joshua-p-williams/ls-pcv-system/docs/open-questions.md

# Open questions

This register coordinates follow-up for unresolved hardware checks and design choices. Component and interface pages retain technical details and final decisions; [project status](status.md) summarizes progress. A documented interface is not a verified connection.

## Start here for W01

**Q01 is resolved:** W01 will define the complete bench wiring for the controller, display, ADC, sensor and conditioning, with phased assembly and verification against that design. See the [W01 scope and assembly approach](../hardware/wiring/README.md#w01-scope-and-assembly). **Q02 is resolved:** W01 uses the N16R8 development board; the XIAO remains the finished-gauge target with its own wiring and verification. **Q03 is resolved:** use one USB source at a time, accepting restart when switching between computer and standalone supply. The N16R8 board has not yet arrived: **Q04** normal board comparison and Q05/Q12 bring-up measurements await receipt; Q30/Q31 resolve the intended bench/display power connections. Q15 selects one multifunction button; Q24 selects the initial gesture mapping. Q23 selects fixed brightness initially with provision for later software configuration and persistent settings. Continue the remaining hardware and wiring choices while retaining provisional hardware assumptions.

The complete bench design requires **Q04-Q10, Q12, Q14-Q18 and Q29** as applicable to the selected controller and interfaces. Converter-powered operation adds **Q11 and Q19**. XIAO-specific **Q13** applies only if that board is used. **Q20-Q22** concern operational validation or later vehicle work; they do not all block drafting a bench harness.

[W01 is now a complete-scope draft](../hardware/wiring/bench/README.md), with proposed assignments, explicit unresolved boundaries and derived assembly views. Assembly-ready connections require the relevant evidence. Tests needing a wired fixture follow verification of its terminal mapping and electrical limits; the register does not require a finished gauge before designing that fixture.

## Design decisions

| ID | Question | How to resolve | Blocks / applies to | Status | Reference / recorded answer |
| --- | --- | --- | --- | --- | --- |
| Q01 | ~~Does W01 begin with controller/display only, or include the ADC and sensor?~~ | Scope selected; retain separate verification questions | W01 scope | Resolved | Complete bench wiring design, including ADC/sensor/conditioning; phased assembly with sectional views and checks derived from the same design. Unknowns marked inline with question IDs. [Recorded approach](../hardware/wiring/README.md#w01-scope-and-assembly) |
| Q02 | ~~Will W01 use the planned N16R8 bench board or a XIAO?~~ | Controller selected; physical verification remains open | W01 controller and pin map | Resolved | N16R8 for W01; XIAO for the finished gauge. Both need complete wiring and phased verification, with explicit firmware board configurations. [Wiring approach](../hardware/wiring/README.md#controller-configurations), [firmware requirements](../firmware/README.md#board-configurations) |
| Q03 | ~~Which power/programming mode will the first bench build use?~~ | Operating choice selected; verify implementation under Q05/Q12 | W01 power topology | Resolved | One USB source at a time: computer for power/debugging or suitable standalone USB supply. Unplugging and restart are acceptable. Full-system USB capacity remains unverified. [Bench power requirements](../hardware/wiring/README.md#bench-power-requirements) |
| Q14 | Which GPIOs serve SPI, I2C, display control and any buttons or ADC-ready signal? | Check the proposed allocation against the actual carrier and preserve memory/boot/debug restrictions; maintain explicit GPIOs in the harness | W01 selected interfaces; XIAO allocation separately | Investigating | [W01 proposed controller table](../hardware/wiring/bench/generated/connections.md#proposed-controller-assignments) allocates eight GPIOs for display, I2C and one button; ALERT is unused under the polling proposal. Actual-board verification pending; [P02](../hardware/pinouts/xiao-esp32s3.md) remains separate |
| Q15 | ~~How many user buttons are included?~~ | Button count selected; original gesture/dimming portions tracked separately as Q24/Q23 | W01 control wiring and pin budget | Resolved | One multifunction button, with BetterButton as the planned input library. GPIO and physical switch remain pending. [Control design](../firmware/README.md#multifunction-button) |
| Q16 | ~~What construction and connection approach should the bench harness use?~~ | Construction policy selected; electrical wire requirements and return routing remain W01 design work | W01 construction guidance | Resolved | On-hand nominal 2.54 mm protoboard/header/socket construction. Use soldered leads or secure removable connections at assembler discretion, with support and strain relief. W01 specifies connectivity and electrical constraints; the build record captures chosen connectors, orientation and lengths. [Recorded requirements](../hardware/wiring/README.md#bench-construction-and-retention) |
| Q17 | How will the selected sensor-input circuit behave, and is further protection needed? | Record actual stock R1/C1; check DC loading, response/noise and shared-supply startup/shutdown; determine any additional protection from the actual operating/fault conditions | Pressure-chain assembly/validation | Investigating | Initial [RC filter](../hardware/components/rc-input-filter/README.md) selected: 470 ohm series, 1 uF nonpolar from OUT to GND, IN/OUT/GND nodes in W01. No divider, buffer or clamp selected; nominal design is not measured performance |
| Q18 | What ADC address, gain, rate, mode and readiness method will be used? | Review the candidate against verified module configuration and signal range, then test fresh-conversion timing | ADC wiring where affected; acquisition bring-up | Investigating | [W01 candidate](../hardware/wiring/bench/README.md#adc-bring-up-candidate): A0 single-ended, ADDR-to-GND / 0x48, selected +/-6.144 V, candidate single-shot 128 SPS, 100 kHz translated I2C and completion polling. No ALERT wire. Physical bias, input limits and effective cadence still require verification |
| Q19 | How will converter-powered operation handle protection, 5 V distribution and USB programming? | Select fuse/protection, distribution and an explicit host-power/backfeed arrangement using verified board/converter paths | Future converter-powered bench work; W05; simultaneous sources excluded from selected W01 mode | Open | [A02](../hardware/architecture/power-system.md), [P06](../hardware/pinouts/buck-converter.md) |
| Q23 | ~~Is adjustable display brightness required for the first build?~~ | Initial policy selected; hardware capability remains Q06 and later menu/storage design is Q26 | Initial display behavior; separated from Q15 | Resolved | Fixed brightness default, with a software configuration option where supported and later persistent in-car settings. No dimming GPIO/circuit selected. [Settings requirements](../firmware/README.md#brightness-and-persistent-settings) |
| Q24 | ~~Which actions should click, double-click and long press perform?~~ | Initial mapping selected; prompt details tracked in Q25 and timing validation remains pending | Button behavior and UI; separated from Q15 | Resolved | Click clears min/max; double-click is unassigned; long press opens atmospheric-zero confirmation without immediately changing zero. [Control design](../firmware/README.md#multifunction-button) |
| Q25 | ~~How does the atmospheric-zero prompt confirm, cancel and time out?~~ | Interaction selected; timeout duration and implementation validation remain tuning work | Zero-confirmation UI; does not change the one-button harness | Resolved | Long press opens the prompt on Cancel; click toggles Cancel/Zero; double-click selects. Inactivity dismisses without changing zero. Prompt reminds the operator to equalize to atmosphere. [Control design](../firmware/README.md#multifunction-button) |
| Q26 | How will the later settings menu and persistent storage work? | Define menu gestures/states, editable settings, defaults, save/cancel and reset behavior; choose an EEPROM-style nonvolatile storage implementation and validate restart recovery | Later firmware/settings UI; no additional button selected | Open | [Settings requirements](../firmware/README.md#brightness-and-persistent-settings) |
| Q27 | ~~Should the ADC remain at 3.3 V with a divider or share 5 V with the sensor?~~ | Architecture selected; implementation and physical checks remain separate | Both controller builds; W01 and measurement chain | Resolved | Shared regulated 5 V sensor/ADS1115 branch, no analog divider, +/-6.144 V range and bidirectional I2C translation to ESP32 3.3 V. [Decision and rationale](../hardware/components/adc/conditioning-review.md) |
| Q28 | ~~Which I2C translator implementation will connect the 3.3 V controller and 5 V ADC buses?~~ | Module and terminal assignment selected; physical pull-up/power checks moved to Q29 | Both controller builds | Resolved | hiBCTR BSS138 module B0DSZBC8K6; 10-pack purchased for USD 6.88. LV=3.3 V, HV=5 V, common ground, channel 1 SDA, channel 2 SCL, no enable GPIO. [Component/terminal reference](../hardware/components/i2c-level-shifter/README.md) |
| Q30 | ~~Which USB port, jumper state and header takeoff supply the W01 bench gauge?~~ | Topology selected from board-family schematic; Q05/Q12 retain normal hardware/load checks | W01 design | Resolved | Native USB / left front view; IN-OUT closed, USB-OTG open; L21 to 5V, L1 to 3V3, L22 common ground. One source, COM unused. [Power/debug plan](../hardware/components/esp32-s3-dev-board/power-plan.md) |
| Q31 | ~~Which rail powers the purchased GC9A01 module?~~ | Supply selected from purchased listing; current/backlight/operation remain Q06/Q12/Q20 | Both controller builds; separate rail budgets | Resolved | 3.3 V VCC and 3.3 V logic; Hosyond listing advertises 3-5 V module supply and ESP32 compatibility. [P05](../hardware/pinouts/gc9a01.md) |

## Hardware verification

Photos, markings and applicable documentation are useful first evidence. Electrical checks need an identified test setup; preserve measured results separately from vendor claims. The linked interface pages describe the checks in detail.

| ID | Question | How to resolve | Blocks / applies to | Status | Reference / recorded answer |
| --- | --- | --- | --- | --- | --- |
| Q04 | Does the received N16R8 board match the adopted listing/family interface? | Compare labeled terminals/orientation during assembly; record build identity and concrete discrepancies without requiring new photos to continue design | Routine as-built comparison; does not block intended wiring | Investigating | YD-family map and V1.4 power circuit adopted as working assumptions for the pictured V1.3 board. [Power plan](../hardware/components/esp32-s3-dev-board/power-plan.md) |
| Q05 | Do the selected N16R8 power/debug paths operate as documented? | During phase 1, check IN-OUT bridge, open USB-OTG, polarity/rails and native USB operation; compare onboard uses as needed | Board bring-up; topology selection resolved in Q30 | Investigating | Native USB and L21 output selected from official family schematic; Q12 retains load margin. [Power plan](../hardware/components/esp32-s3-dev-board/power-plan.md) |
| Q06 | What current/backlight behavior and operating limits does the display demonstrate at the selected 3.3 V supply? | Use listing range and ESP32 compatibility as working basis; check current, operation and any supported dimming during bring-up | Display validation and regulator budget; supply selection resolved in Q31 | Investigating | Hosyond listing specifies 3-5 V power; VCC and SPI/control selected at 3.3 V. No dimming GPIO selected. [P05](../hardware/pinouts/gc9a01.md) |
| Q07 | Is the ADC actually an ADS1115, and does its header match P03? | Record IC/PCB markings and verify header connectivity; corroborate conversion format/timing during bring-up | ADC wiring and acquisition assumptions | Open | [P03](../hardware/pinouts/ads1115.md) |
| Q08 | What pull-ups, ADDR bias and decoupling are fitted to the ADC module? | Inspect/measure unpowered circuitry; verify rail and idle bus levels in a documented setup | I2C/address wiring and Q18 | Open | [P03 power and logic](../hardware/pinouts/ads1115.md#power-logic-and-analog-boundary) |
| Q09 | Which sensor cavities are supply, return and output, and which pigtail leads reach them? | Use the adopted GM-family map; complete lead continuity/fit check during assembly | As-built sensor lead identification; design may proceed with adopted map | Investigating | [P04](../hardware/pinouts/ftp-sensor.md): pigtail mating face, latch up, left A=ground, center B=signal, right C=5 V. GM document 1706435 p.19 adopted as working assumption; W01 updated. Pigtail arrival/lead check remains pending |
| Q10 | What supply, output, pressure and atmospheric-reference limits apply to the actual FTP sensor? | Use sourced replacement-family expectations as working assumptions; check response during bring-up and calibrate before reporting pressure accuracy | Final test limits and calibration; preliminary conditioning may proceed with explicit assumptions | Investigating | Nominal 5 V, three-wire analog interface adopted for design; output/pressure expectations remain research work. [P04](../hardware/pinouts/ftp-sensor.md) |
| Q11 | Does the converter match its label, and how do its output, returns and USB-C connection behave? | Record actual unit; verify polarity, intended adapter mapping, return relationships and output/load behavior in a suitable fixture | Converter-powered bench build and vehicle power | Open | [P06 verification](../hardware/pinouts/buck-converter.md#verification-before-harness-design) |
| Q12 | Can the selected board and source supply the intended peripheral load? | Establish applicable ratings; measure rails and startup/operating loads progressively, including display activity and controller consumption | Connecting selected loads; final power budget | Open | [A02 rail responsibilities](../hardware/architecture/power-system.md#rail-and-load-responsibilities) |
| Q13 | Which XIAO revision is present, and what regulator and USB/VBUS limits apply? | Record board markings; match a schematic, reconcile the 600/700 mA references and verify relevant power paths | XIAO build only; does not block an N16R8-only harness | Open | [P02 power interfaces](../hardware/pinouts/xiao-esp32s3.md#power-interfaces) |
| Q20 | What initialization/configuration makes the display work correctly and read clearly? | Record driver/version, reset and SPI settings; test colors, rotation, clipping and viewing position | Display bring-up and final display/enclosure choice; not basic header identification | Open | [P05 bring-up](../hardware/pinouts/gc9a01.md#controller-allocation-and-bring-up) |
| Q21 | What calibration and response does the complete measurement chain achieve? | Record known-pressure points, zero/slope/repeatability, acquisition timing, peaks and fault behavior with the exact configuration | Valid pressure readings and vehicle tuning; follows a verified bench fixture | Open | [Test plan](testing/test-plan.md), [A03](../hardware/architecture/measurement-system.md) |
| Q22 | How will the pressure tap, sensor reference/vent, hose and mounting be implemented? | Confirm actual PCV ports and routing; select sealing/retention and protect from liquids while preserving the required pressure reference | Installed pressure measurement; W05 and mounting work | Open | [A04](../hardware/architecture/pcv-system.md), [P04 pressure interface](../hardware/pinouts/ftp-sensor.md#pressure-interface-and-calibration) |
| Q29 | How do the assembled translator and ADC pull-ups, bus levels and power transitions behave? | Account for fitted pull-ups, check orientation/ground, LV/HV and idle levels, then communication at 100 kHz and startup/shutdown in the selected single-source mode | ADC bus bring-up on each controller configuration; complements Q08 | Open | [Translator bring-up](../hardware/components/i2c-level-shifter/README.md#pull-ups-and-bring-up). Module selection is resolved under Q28; receipt/operation not reported |

## Maintaining the register

- Keep IDs stable; append new IDs without renumbering existing entries. Grouping and display order may change as dependencies become clearer.
- Use **Open**, **Investigating** or **Resolved**. Mark Investigating when evidence collection or evaluation actually begins. If a question becomes inapplicable, record the scope decision and resolve it with that explanation.
- Record the answer, rationale and evidence in the relevant component/interface document first, then add a brief answer/link here and update status. Strike through the question text when resolved; retain the ID, status and readable answer so references stay useful.
- A design selection can resolve a decision without proving hardware behavior. Keep associated verification questions open until their own evidence exists.
- Place new photos or source documents in `_staging/inbox/<batch>/` for review and sanitized import. Public answers must link to public project records, not ignored staging files. For measurements, use the [data conventions](../data/README.md).
- Update affected harnesses and [project status](status.md) when answers change their readiness. This register tracks follow-up, not every implementation task or historical assumption.
