joshua-p-williams/ls-pcv-system/cad/pcv-restrictor/import-2026-10-05.md

# Restrictor import - 2026-10-05

## Provenance and placement

Source: supplied `PCV-Restrictor` batch containing a README, native FreeCAD model, three 3MF files, and two PNG model views. Inbox originals were preserved. The public [component README](README.md) incorporates the useful design and printing notes while distinguishing intentions from verified geometry.

Native source is in `source/`; all three 3MF variants are together in `printing/`. The 2 mm file is a FreeCAD mesh export; the 3 and 4 mm files are QIDI Studio projects with print settings. Supplied views are in `media/diagrams/pcv-restrictor/`. The variants were consolidated on 2026-10-06 without changing file contents.

## Privacy and preservation

- Reviewed notes, image content, embedded previews, archive metadata, and text/configuration members for personal information and local paths. No visible personal identifiers were observed in model views or previews.
- Cleared FreeCAD author/company/comment/date metadata fields; populated creation/modification timestamps were removed. License metadata was preserved.
- Removed QIDI project descriptive/designer/date metadata from top-level model XML. Application/version metadata, licensing fields, geometry, transforms, project settings, and internal relationships were preserved.
- Stripped metadata from public PNGs and embedded PNG previews without changing decoded pixels. ZIP timestamps were normalized and archive comments omitted.
- Compared all archive members: native geometry payloads and slicer configuration files are byte-identical to the supplied versions; 3MF geometry/resources/build structures are unchanged after excluding descriptive metadata.
- Normalized public filenames. No generative image edits, geometry edits, new slicing, or additional exports were performed.

## Validation performed

Original and public native files were opened and fully recomputed without saving in installed FreeCAD **1.1.1**. The file header reports `1.1R20260414 (Git shallow)`.

| Native model check | Result |
| --- | --- |
| Solid count | 1 |
| Shape validity | Valid |
| Object invalid states | None reported |
| Bounding dimensions | 14 x 14 x 67 mm |
| Volume | 5264.479041921313 mm³ |
| Volume change after full recompute | 0 mm³ |
| Metering cylinder | 3 mm ID, 3 mm axial length |

Each mesh contains 4,158 vertices and 8,316 triangles. Coordinates are finite, indices are in range, and every undirected edge occurs twice. Units are explicitly millimeters. Minimum radial vertex coordinates support the labeled 2, 3, and 4 mm bores; all have a 3 mm metering length. Native/source coordinates span Z = -32 to +35 mm; QIDI local meshes are centered at -33.5 to +33.5 mm, with placement transforms retained.

ZIP integrity, XML parsing, sanitized PNG pixel equality, and unchanged geometry payloads were checked. Native inspection establishes the dimension discrepancies recorded in the [component README](README.md).

Not performed: GUI review of the editable feature tree, slicer open/slice validation, full mesh self-intersection testing, physical dimensional inspection, flow testing, temperature/material qualification, or vehicle testing. Source revision and tessellation settings for each supplied export remain unknown; files were imported rather than regenerated.

## Imported artifact fingerprints

SHA-256 of sanitized public artifacts at import; subsequent intentional revisions will change these hashes.

| Artifact | SHA-256 |
| --- | --- |
| `source/pcv-restrictor.FCStd` | `3a3ae540264c3b71b7e548aaa10d7c7bbf83c59d6f2fed069d197a060f7b6cd8` |
| `printing/pcv-restrictor-2mm.3mf` | `02f1d0feda57187e146a3ce807ca8a6f50e7bbc778df6cfdd2fcbdabf9f16f2c` |
| `printing/pcv-restrictor-3mm.3mf` | `d005f78b86c65b54239de37e1c21f5e4add04a9eac168d750e66ddfe86bee9d3` |
| `printing/pcv-restrictor-4mm.3mf` | `dcb3687ee4a393515e752b3c1172a6e232f71b5579973f324cbdb4961428aa7d` |
| `pcv-restrictor-isometric.png` in public diagrams | `cd9594a8c6048ca62f70921db02a6a71bfa333954e3a7740a32146a1c36445e3` |
| `pcv-restrictor-side.png` in public diagrams | `38c2c0d426ac9196a969d9ff14de747904160374d2697ebc40acca10bbc40084` |
