joshua-p-williams/ls-pcv-system/media/reference/gauge-electronics/bench-board/component-callouts.png

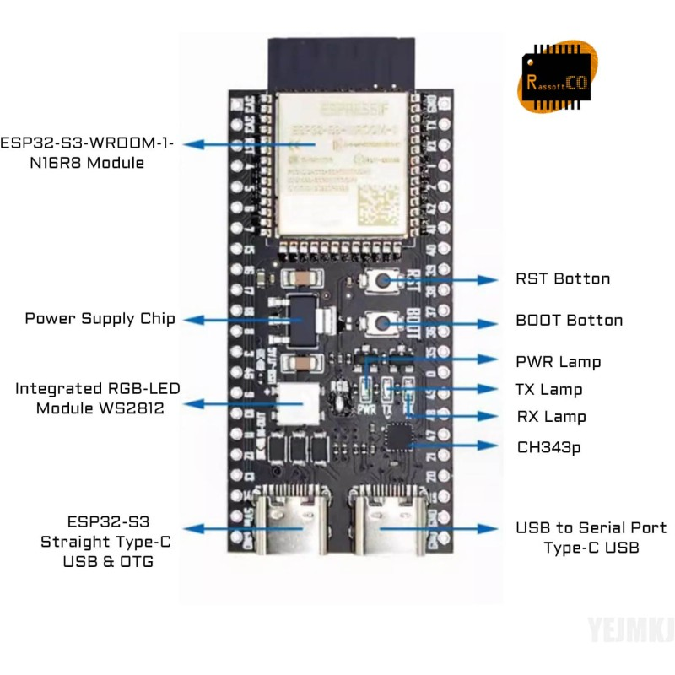
media/reference/gauge-electronics/bench-board/component-callouts.png
